10robert03/stm32-nrf24-usb-node/Screenshots/power_supply_wiring.png

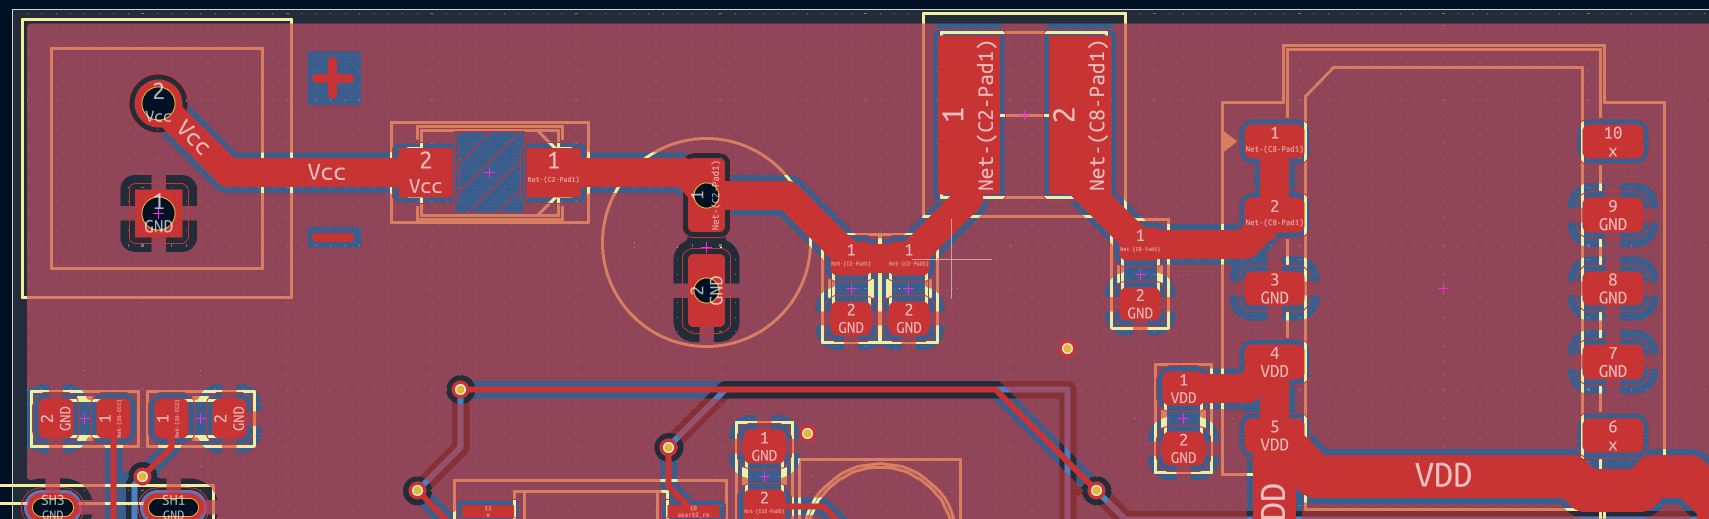
Screenshots/power_supply_wiring.png
