10robert03/stm32-nrf24-usb-node/Screenshots/stm32_spi_oscillator_wiring.png

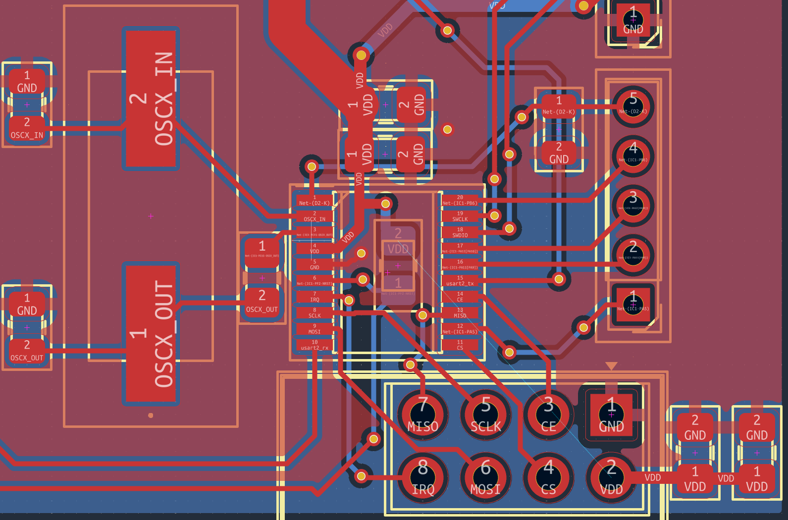
Screenshots/stm32_spi_oscillator_wiring.png
