10robert03/stm32-nrf24-usb-node/Screenshots/USB_C_wiring.png

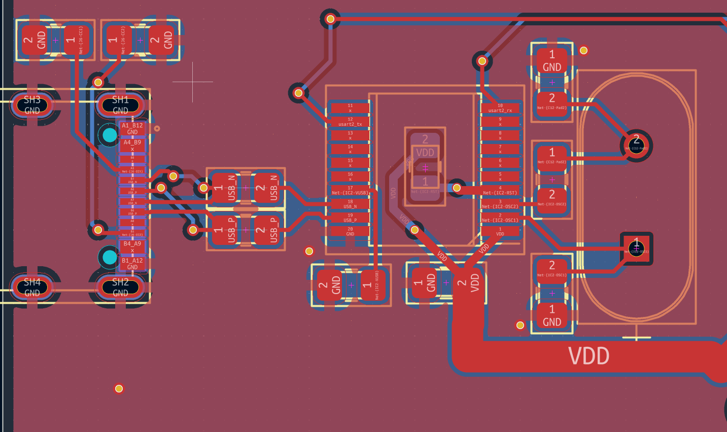
Screenshots/USB_C_wiring.png
